helmarw/10inch-Rack-SDR-Station/photos/IMG_1468.jpg

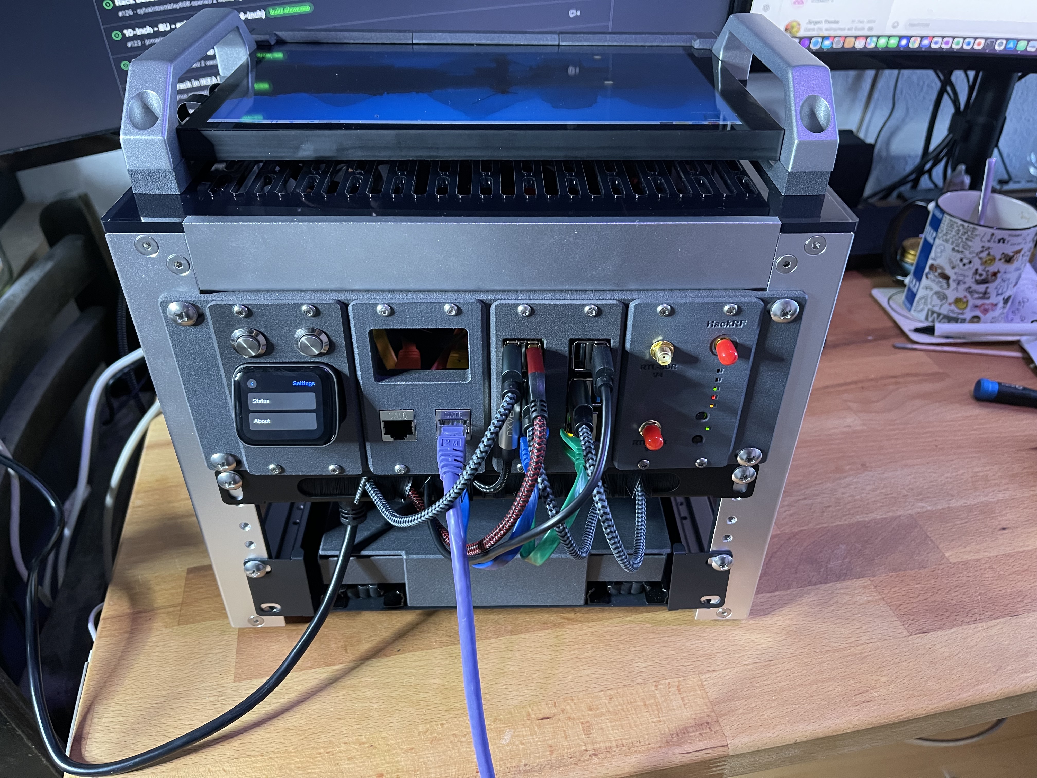
photos/IMG_1468.jpg
