helmarw/10inch-Rack-SDR-Station/CAD/Module 1x SDR 2x RTL 1x HackRF.step

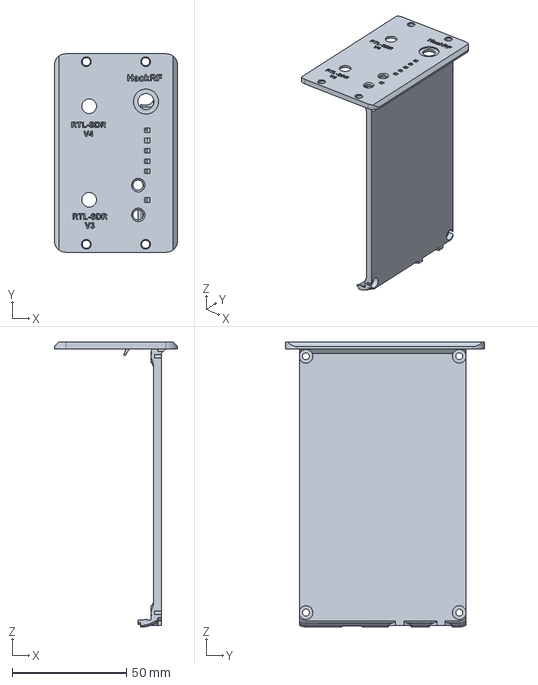
[picture p21: CAD file, 2025-02-20]
CAD/Module 1x SDR 2x RTL 1x HackRF.step
54.0 x 87.0 x 124.9 mm
